Xtra-Large/GpsN2KWifiGateaway/N2kDataToNMEA0183.cpp

/*
N2kDataToNMEA0183.cpp

Copyright (c) 2015-2018 Timo Lappalainen, Kave Oy, www.kave.fi

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
THE SOFTWARE IS PROVIDED "AS IS", WITHOUT WARRANTY OF ANY KIND, EXPRESS OR IMPLIED,
INCLUDING BUT NOT LIMITED TO THE WARRANTIES OF MERCHANTABILITY, FITNESS FOR A
PARTICULAR PURPOSE AND NONINFRINGEMENT. IN NO EVENT SHALL THE AUTHORS OR COPYRIGHT
HOLDERS BE LIABLE FOR ANY CLAIM, DAMAGES OR OTHER LIABILITY, WHETHER IN AN ACTION OF
CONTRACT, TORT OR OTHERWISE, ARISING FROM, OUT OF OR IN CONNECTION WITH THE SOFTWARE
OR THE USE OR OTHER DEALINGS IN THE SOFTWARE.
*/

#include "N2kDataToNMEA0183.h"
#include <N2kMessages.h>
#include <NMEA0183Messages.h>
#include <math.h>


const double radToDeg=180.0/M_PI;

//*****************************************************************************
void tN2kDataToNMEA0183::HandleMsg(const tN2kMsg &N2kMsg) {
  switch (N2kMsg.PGN) {
    case 126992UL: HandleSystemDateTime(N2kMsg);
    case 127250UL: HandleHeading(N2kMsg);
    case 127258UL: HandleVariation(N2kMsg);
    case 128259UL: HandleBoatSpeed(N2kMsg);
    case 128267UL: HandleDepth(N2kMsg);
    case 129025UL: HandlePosition(N2kMsg);
    case 129026UL: HandleCOGSOG(N2kMsg);
    case 129029UL: HandleGNSS(N2kMsg);
    case 130306UL: HandleWind(N2kMsg);
  }
}

//*****************************************************************************
void tN2kDataToNMEA0183::Update() {
  SendRMC();
  if ( LastHeadingTime+2000<millis() ) Heading=N2kDoubleNA;
  if ( LastCOGSOGTime+2000<millis() ) { COG=N2kDoubleNA; SOG=N2kDoubleNA; }
  if ( LastPositionTime+4000<millis() ) { Latitude=N2kDoubleNA; Longitude=N2kDoubleNA; }
  if ( LastWindTime+2000<millis() ) { WindSpeed=N2kDoubleNA; WindAngle=N2kDoubleNA; }
}

//*****************************************************************************
void tN2kDataToNMEA0183::SendMessage(const tNMEA0183Msg &NMEA0183Msg) {
  if ( pNMEA0183!=0 ) pNMEA0183->SendMessage(NMEA0183Msg);
  if ( SendNMEA0183MessageCallback!=0 ) SendNMEA0183MessageCallback(NMEA0183Msg);
}

//*****************************************************************************
void tN2kDataToNMEA0183::HandleSystemDateTime(const tN2kMsg& N2kMsg) {
unsigned char SID;
uint16_t SystemDate;
double SystemTime;
tN2kTimeSource TimeSource;
tNMEA0183Msg NMEA0183Msg;

  if (ParseN2kSystemTime(N2kMsg, SID, SystemDate, SystemTime, TimeSource)) {
      time_t t = tNMEA0183Msg::daysToTime_t(SystemDate);
      tmElements_t tm;
      tNMEA0183Msg::breakTime(t, tm);
      int GPSDay = tNMEA0183Msg::GetDay(tm);
      int GPSMonth = tNMEA0183Msg::GetMonth(tm);
      int GPSYear = tNMEA0183Msg::GetYear(tm);
      int LZD = 0;
      int LZMD = 0;
      if (NMEA0183SetZDA(NMEA0183Msg, SystemTime, GPSDay, GPSMonth, GPSYear, LZD, LZMD, "GP")) {
          SendMessage(NMEA0183Msg);
      }
  }
}

//*****************************************************************************
void tN2kDataToNMEA0183::HandleHeading(const tN2kMsg &N2kMsg) {
unsigned char SID;
tN2kHeadingReference ref;
double _Deviation=0;
double _Variation;
tNMEA0183Msg NMEA0183Msg;

  if ( ParseN2kHeading(N2kMsg, SID, Heading, _Deviation, _Variation, ref) ) {
    if ( ref==N2khr_magnetic ) {
      if ( !N2kIsNA(_Variation) ) Variation=_Variation; // Update Variation
      if ( !N2kIsNA(Heading) && !N2kIsNA(Variation) ) Heading-=Variation;
    }
    LastHeadingTime=millis();
    if ( NMEA0183SetHDG(NMEA0183Msg,Heading,_Deviation,Variation) ) {
      SendMessage(NMEA0183Msg);
    }
  }
}

//*****************************************************************************
void tN2kDataToNMEA0183::HandleVariation(const tN2kMsg &N2kMsg) {
unsigned char SID;
tN2kMagneticVariation Source;

  ParseN2kMagneticVariation(N2kMsg,SID,Source,DaysSince1970,Variation);
}

//*****************************************************************************
void tN2kDataToNMEA0183::HandleBoatSpeed(const tN2kMsg &N2kMsg) {
unsigned char SID;
double WaterReferenced;
double GroundReferenced;
tN2kSpeedWaterReferenceType SWRT;

  if ( ParseN2kBoatSpeed(N2kMsg,SID,WaterReferenced,GroundReferenced,SWRT) ) {
    tNMEA0183Msg NMEA0183Msg;
    double MagneticHeading=( !N2kIsNA(Heading) && !N2kIsNA(Variation)?Heading+Variation: NMEA0183DoubleNA);
    if ( NMEA0183SetVHW(NMEA0183Msg,Heading,MagneticHeading,WaterReferenced) ) {
      SendMessage(NMEA0183Msg);
    }
  }
}

//*****************************************************************************
void tN2kDataToNMEA0183::HandleDepth(const tN2kMsg &N2kMsg) {
unsigned char SID;
double DepthBelowTransducer;
double Offset;
double Range;

  if ( ParseN2kWaterDepth(N2kMsg,SID,DepthBelowTransducer,Offset,Range) ) {
      tNMEA0183Msg NMEA0183Msg;
      if ( NMEA0183SetDPT(NMEA0183Msg,DepthBelowTransducer,Offset) ) {
        SendMessage(NMEA0183Msg);
      }
      if ( NMEA0183SetDBx(NMEA0183Msg,DepthBelowTransducer,Offset) ) {
        SendMessage(NMEA0183Msg);
      }
  }
}

//*****************************************************************************
void tN2kDataToNMEA0183::HandlePosition(const tN2kMsg &N2kMsg) {

  if ( ParseN2kPGN129025(N2kMsg, Latitude, Longitude) ) {
    LastPositionTime=millis();
  }
}

//*****************************************************************************
void tN2kDataToNMEA0183::HandleCOGSOG(const tN2kMsg &N2kMsg) {
unsigned char SID;
tN2kHeadingReference HeadingReference;
tNMEA0183Msg NMEA0183Msg;

  if ( ParseN2kCOGSOGRapid(N2kMsg,SID,HeadingReference,COG,SOG) ) {
    LastCOGSOGTime=millis();
    double MCOG=( !N2kIsNA(COG) && !N2kIsNA(Variation)?COG-Variation:NMEA0183DoubleNA );
    if ( HeadingReference==N2khr_magnetic ) {
      MCOG=COG;
      if ( !N2kIsNA(Variation) ) COG-=Variation;
    }
    if ( NMEA0183SetVTG(NMEA0183Msg,COG,MCOG,SOG) ) {
      SendMessage(NMEA0183Msg);
    }
  }
}

//*****************************************************************************
void tN2kDataToNMEA0183::HandleGNSS(const tN2kMsg &N2kMsg) {
unsigned char SID;
tN2kGNSStype GNSStype;
tN2kGNSSmethod GNSSmethod;
unsigned char nSatellites;
double HDOP;
double PDOP;
double GeoidalSeparation;
unsigned char nReferenceStations;
tN2kGNSStype ReferenceStationType;
uint16_t ReferenceSationID;
double AgeOfCorrection;
tNMEA0183Msg NMEA0183Msg;

  if ( ParseN2kGNSS(N2kMsg,SID,DaysSince1970,SecondsSinceMidnight,Latitude,Longitude,Altitude,GNSStype,GNSSmethod,
                    nSatellites,HDOP,PDOP,GeoidalSeparation,
                    nReferenceStations,ReferenceStationType,ReferenceSationID,AgeOfCorrection) ) {
    LastPositionTime=millis();
    if (NMEA0183SetGGA(NMEA0183Msg, SecondsSinceMidnight, Latitude, Longitude, static_cast<uint32_t>(GNSSmethod), nSatellites, HDOP, Altitude, GeoidalSeparation, AgeOfCorrection, ReferenceSationID== N2kInt16NA ? NMEA0183UInt32NA : ReferenceSationID)) {
        SendMessage(NMEA0183Msg);
    }
  }
}

//*****************************************************************************
void tN2kDataToNMEA0183::HandleWind(const tN2kMsg &N2kMsg) {
unsigned char SID;
tN2kWindReference WindReference;
tNMEA0183WindReference NMEA0183Reference=NMEA0183Wind_True;

  if ( ParseN2kWindSpeed(N2kMsg,SID,WindSpeed,WindAngle,WindReference) ) {
    tNMEA0183Msg NMEA0183Msg;
    LastWindTime=millis();
    if ( WindReference==N2kWind_Apparent ) NMEA0183Reference=NMEA0183Wind_Apparent;

    if ( NMEA0183SetMWV(NMEA0183Msg, WindAngle*radToDeg, NMEA0183Reference , WindSpeed) ) {
      SendMessage(NMEA0183Msg);
    }
  }
}

//*****************************************************************************
void tN2kDataToNMEA0183::SendRMC() {
    if ( NextRMCSend<=millis() && !N2kIsNA(Latitude) ) {
      tNMEA0183Msg NMEA0183Msg;
      if ( NMEA0183SetRMC(NMEA0183Msg,SecondsSinceMidnight,Latitude,Longitude,COG,SOG,DaysSince1970,Variation) ) {
        SendMessage(NMEA0183Msg);
      }
      SetNextRMCSend();
    }
}
